ASUMobiCarG11/ASUMobiCarG11/Arduino EX - SH/1.PNG

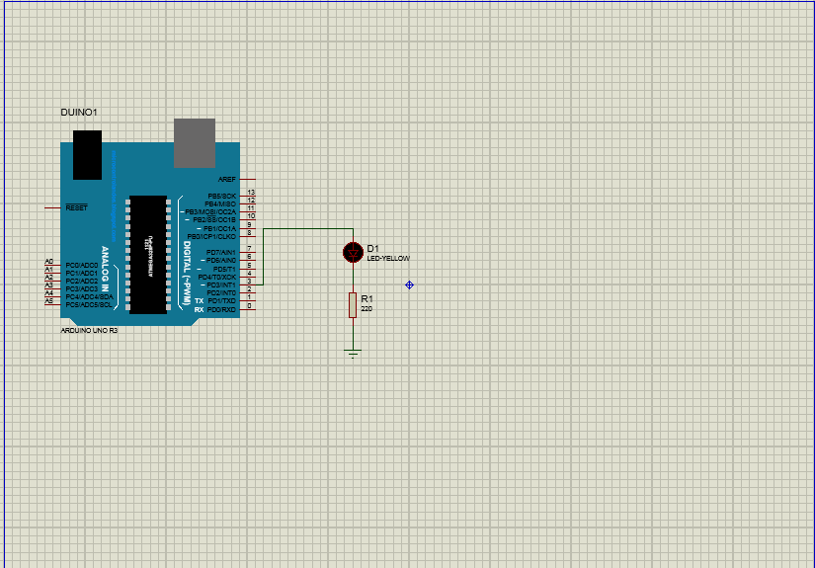
Arduino EX - SH/1.PNG
