ASUMobiCarG11/ASUMobiCarG11/Arduino EX - SH/Q2.PNG

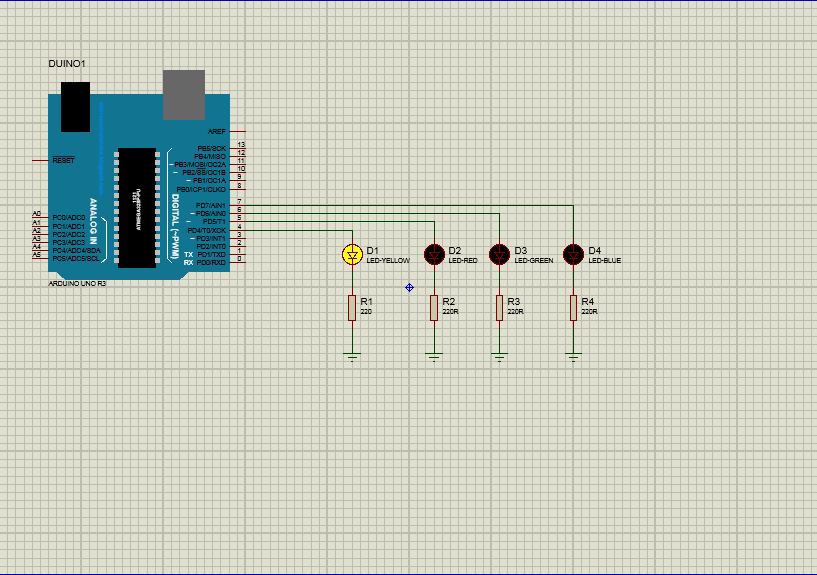
Arduino EX - SH/Q2.PNG
