ASUMobiCarG11/ASUMobiCarG11/Designing the car/re-car-final.jpg

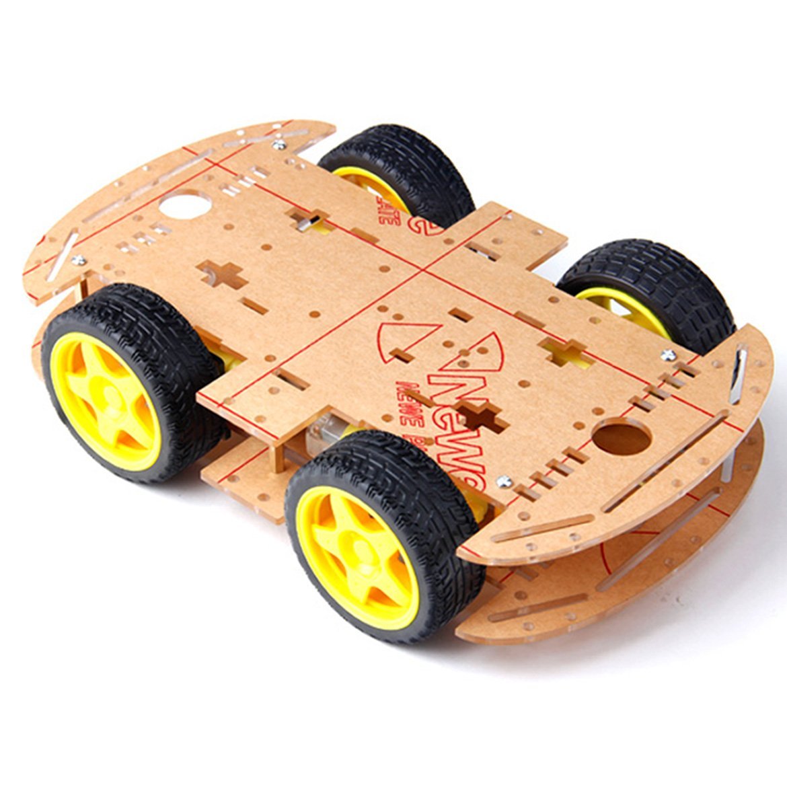
Designing the car/re-car-final.jpg
