ASUMobiCarG11/ASUMobiCarG11/dfrobot-4wd-arduino-mobile-platform-2_2.jpg

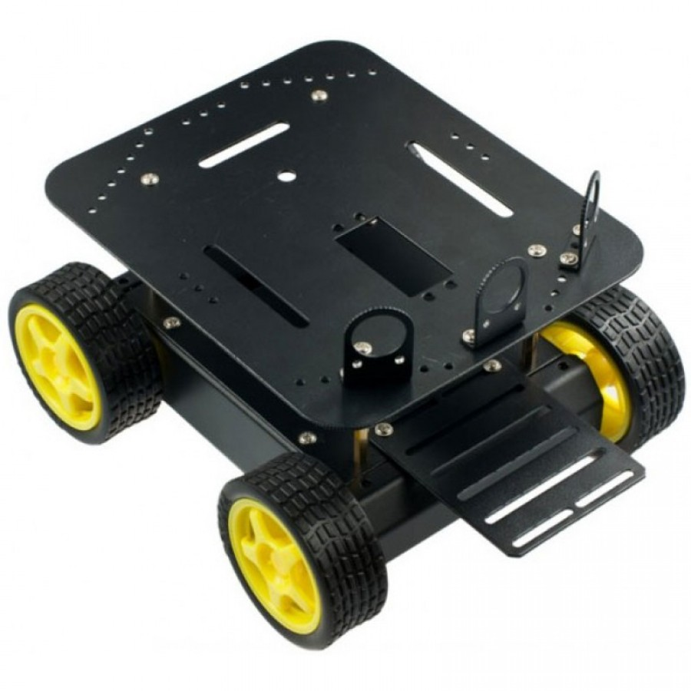
dfrobot-4wd-arduino-mobile-platform-2_2.jpg
