ASUMobiCarG11/ASUMobiCarG11/images.jpg

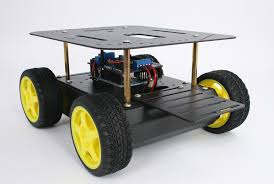
images.jpg
