ASUMobiCarG11/ASUMobiCarG11/Sheet1 Q1.JPG

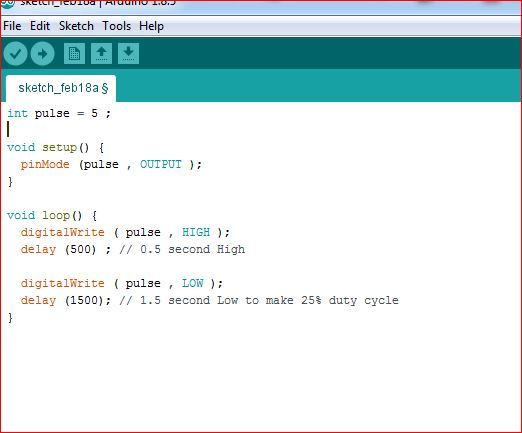
Sheet1 Q1.JPG
