ASUMobiCarG11/ASUMobiCarG11/The code/line follower/all if conditions of line follower.jpg

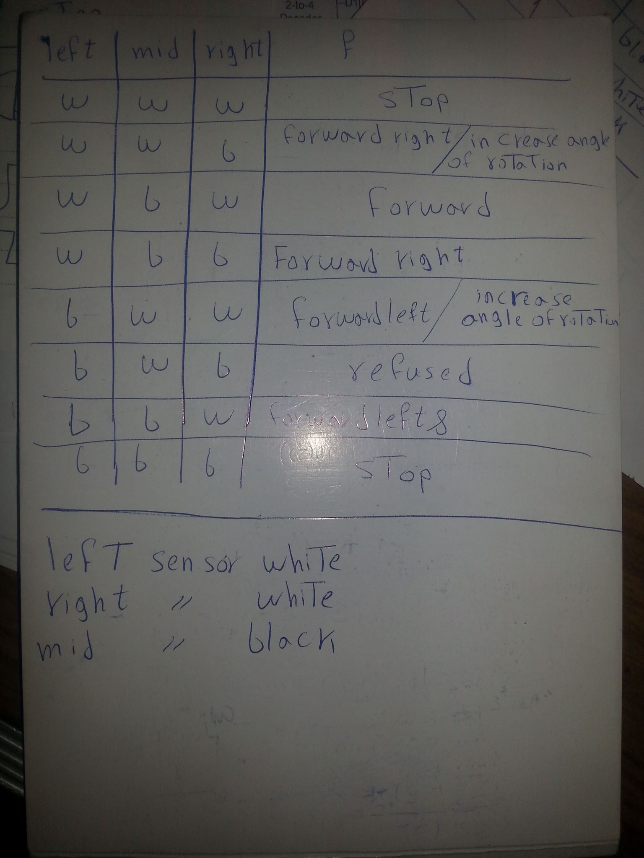
The code/line follower/all if conditions of line follower.jpg
