ASUMobiCarG11/ASUMobiCarG11/Components/3 Line Follower Sensors.jpg

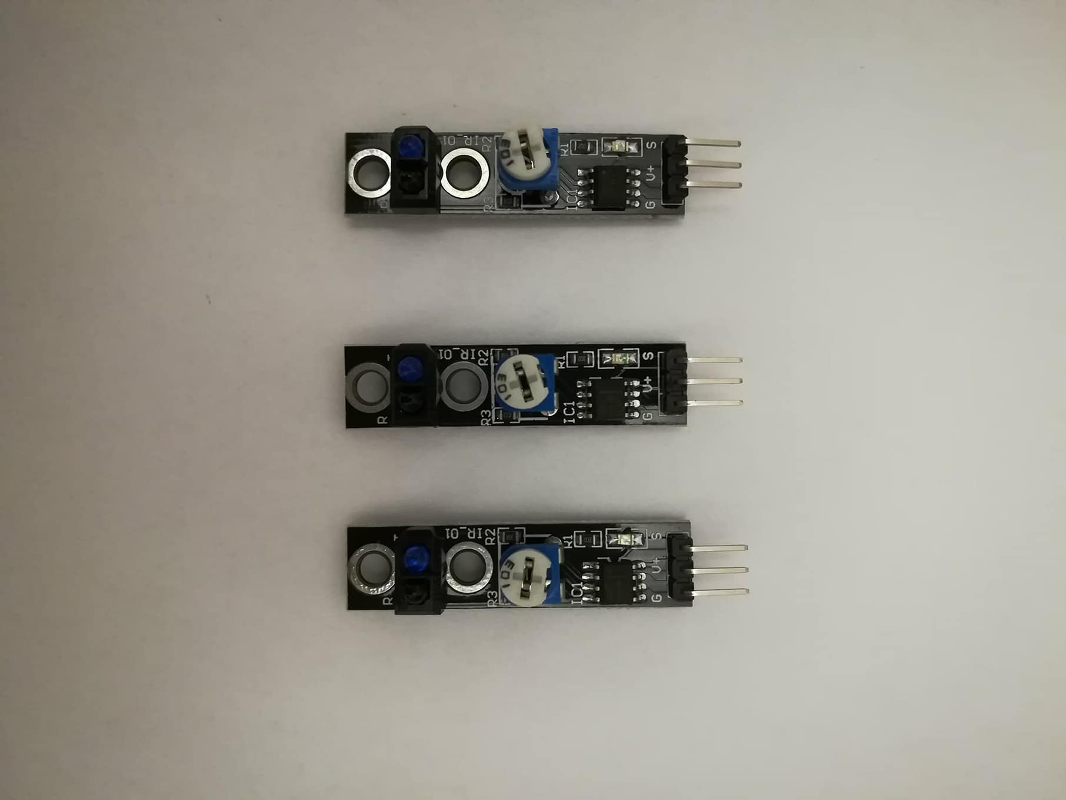
Components/3 Line Follower Sensors.jpg
