ASUMobiCarG11/ASUMobiCarG11/Components/battery.jpeg

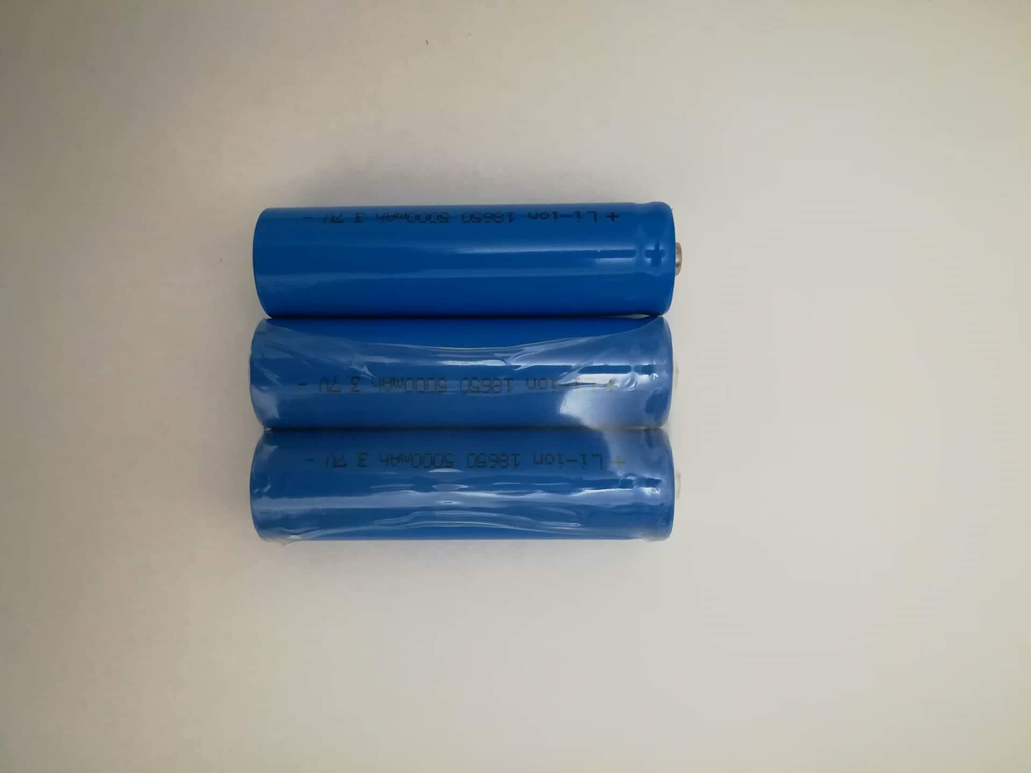
Components/battery.jpeg
