ASUMobiCarG11/ASUMobiCarG11/Components/body of cr.jpeg

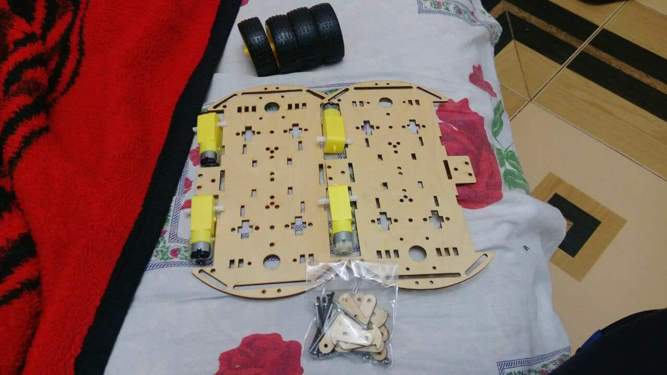
Components/body of cr.jpeg
