ASUMobiCarG11/ASUMobiCarG11/Components/charger.jpeg

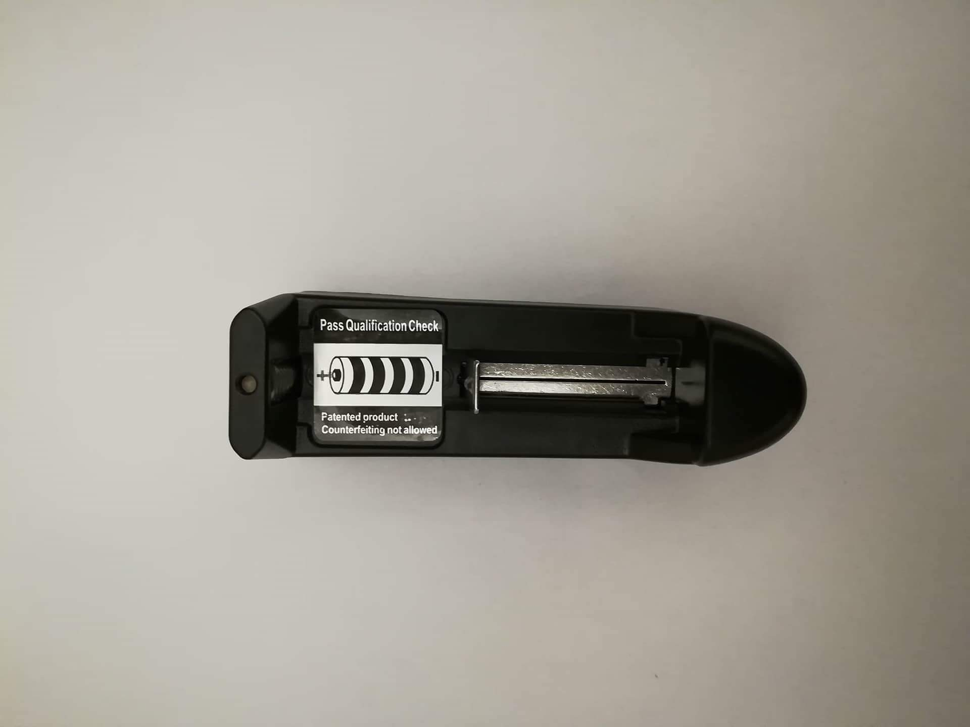
Components/charger.jpeg
