ASUMobiCarG11/ASUMobiCarG11/Components/ultra sonic holder.jpg

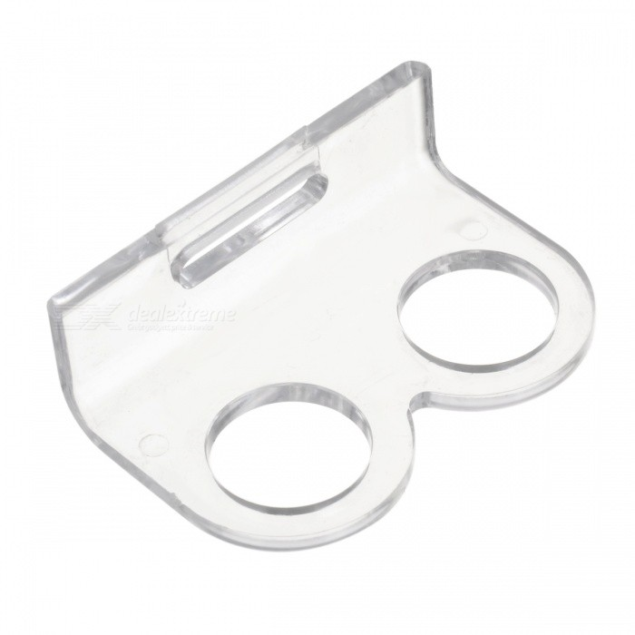
Components/ultra sonic holder.jpg
