ASUMobiCarG11/ASUMobiCarG11/Car installation step by step/instaliing motors to body 1.jpg

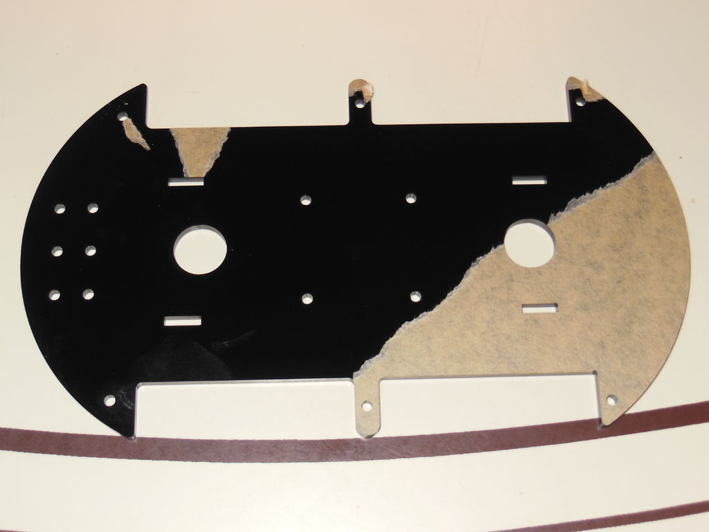
Car installation step by step/instaliing motors to body 1.jpg
