ASUMobiCarG11/ASUMobiCarG11/Car installation step by step/instaliing motors to body 3 invert.jpg

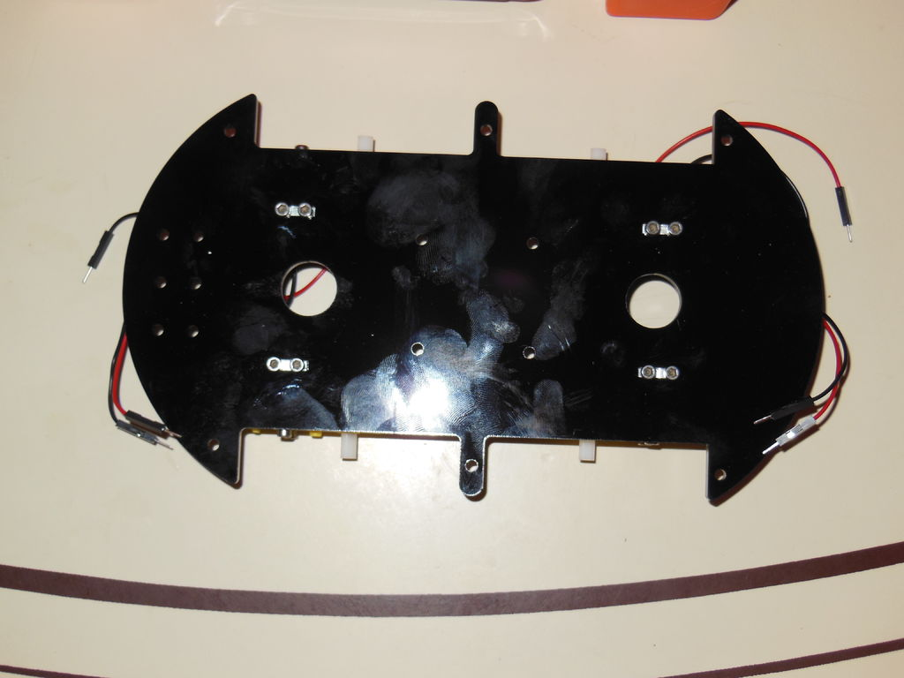
Car installation step by step/instaliing motors to body 3 invert.jpg
