ASUMobiCarG11/ASUMobiCarG11/Car installation step by step/installing arduino uno.jpg

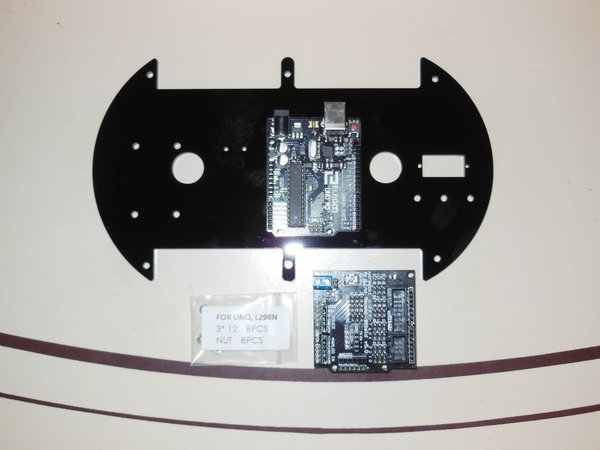
Car installation step by step/installing arduino uno.jpg
