ASUMobiCarG11/ASUMobiCarG11/Car installation step by step/installing battery.jpg

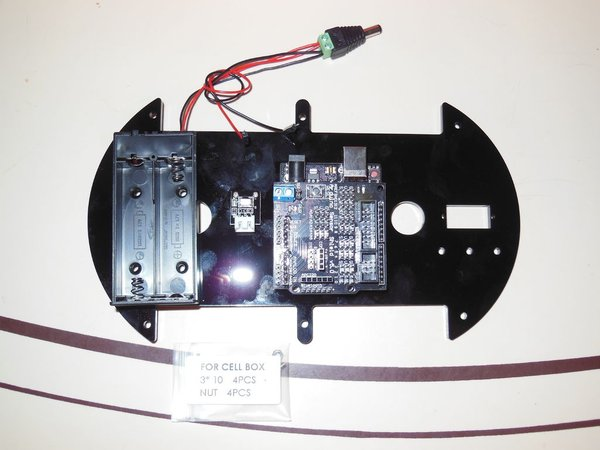
Car installation step by step/installing battery.jpg
