ASUMobiCarG11/ASUMobiCarG11/Car installation step by step/installing blutooth module.jpg

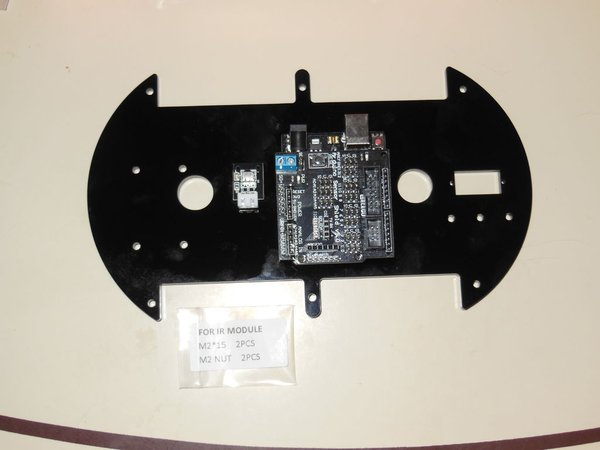
Car installation step by step/installing blutooth module.jpg
