ASUMobiCarG11/ASUMobiCarG11/Car installation step by step/installing line tracker 1.jpg

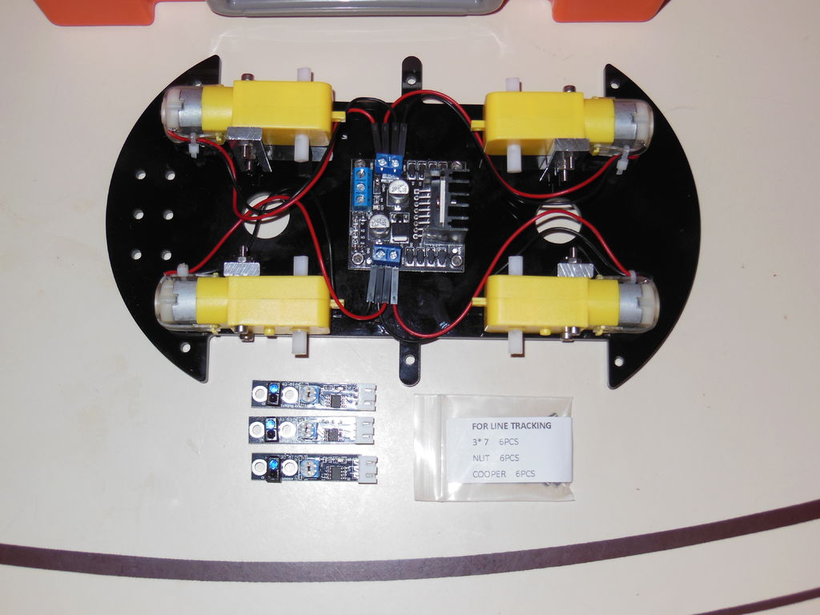
Car installation step by step/installing line tracker 1.jpg
