ASUMobiCarG11/ASUMobiCarG11/Car installation step by step/installing mototr driver 2.jpg

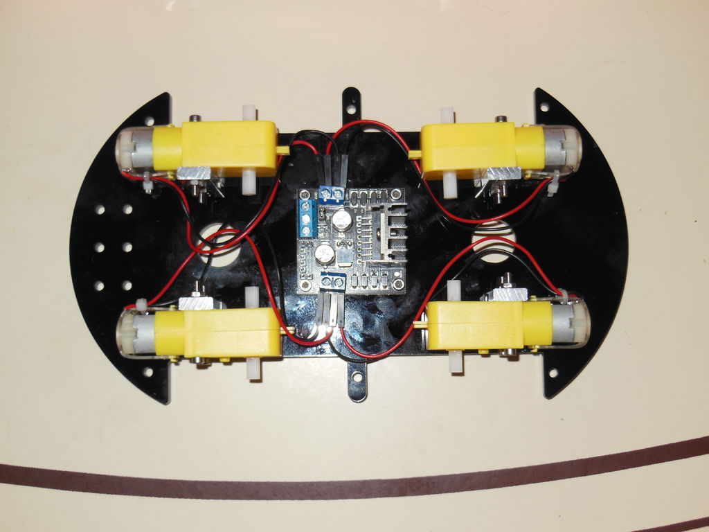
Car installation step by step/installing mototr driver 2.jpg
