ASUMobiCarG11/ASUMobiCarG11/Car installation step by step/ready1.jpg

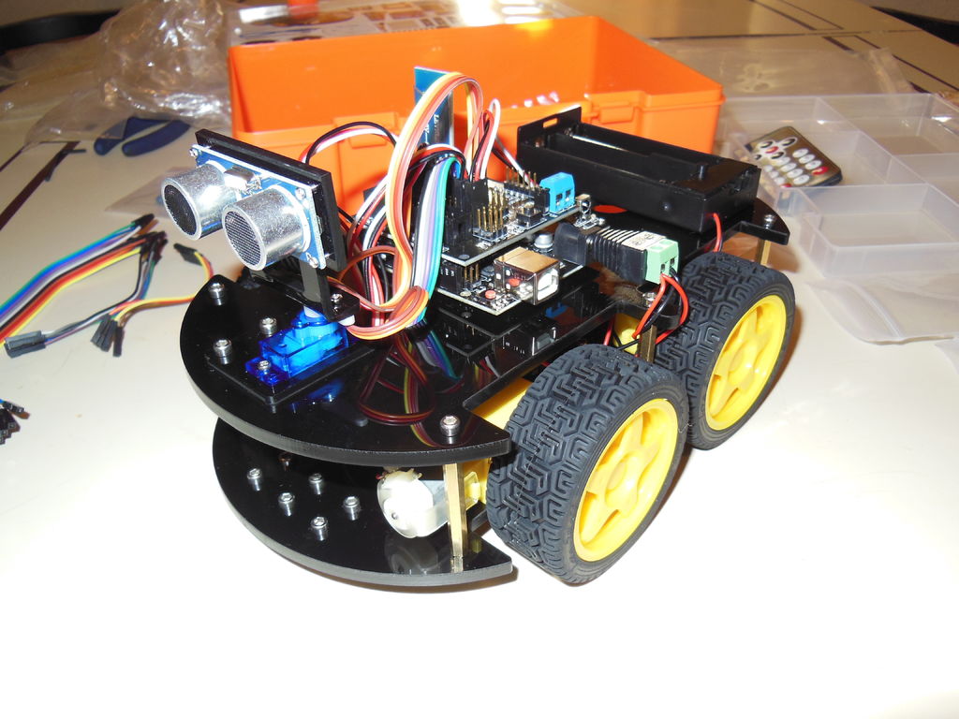
Car installation step by step/ready1.jpg
