ASUMobiCarG11/ASUMobiCarG11/Car installation step by step/ready2.jpg

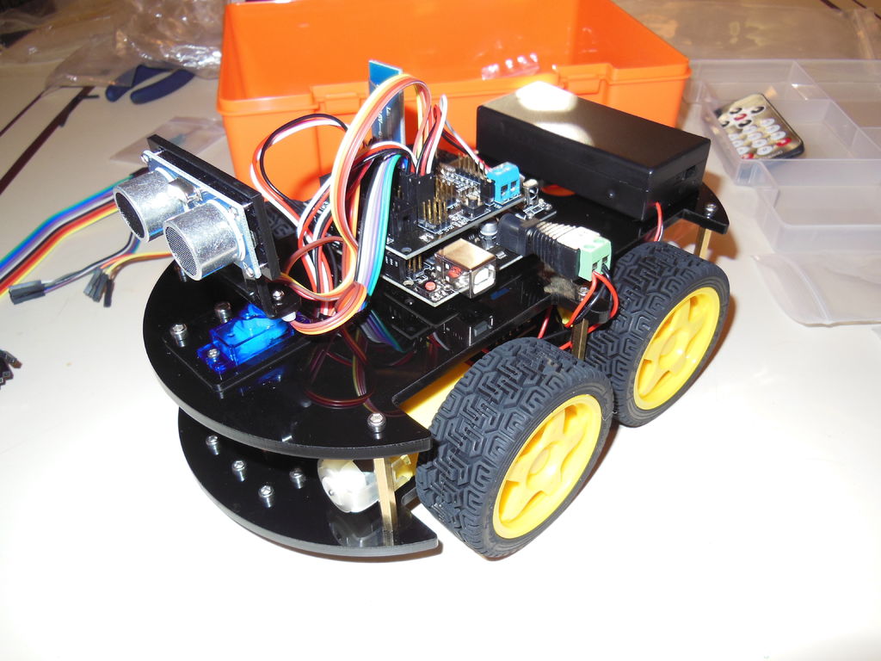
Car installation step by step/ready2.jpg
