ASUMobiCarG11/ASUMobiCarG11/Car installation step by step/ready3.jpg

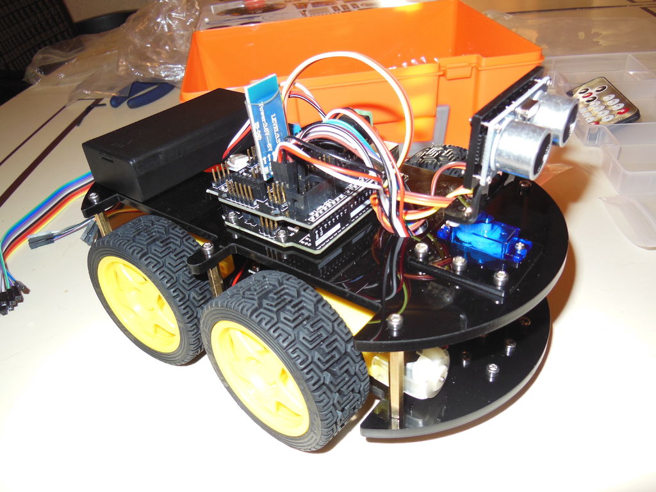
Car installation step by step/ready3.jpg
