ASUMobiCarG11/ASUMobiCarG11/step(1) _design by buttons.png

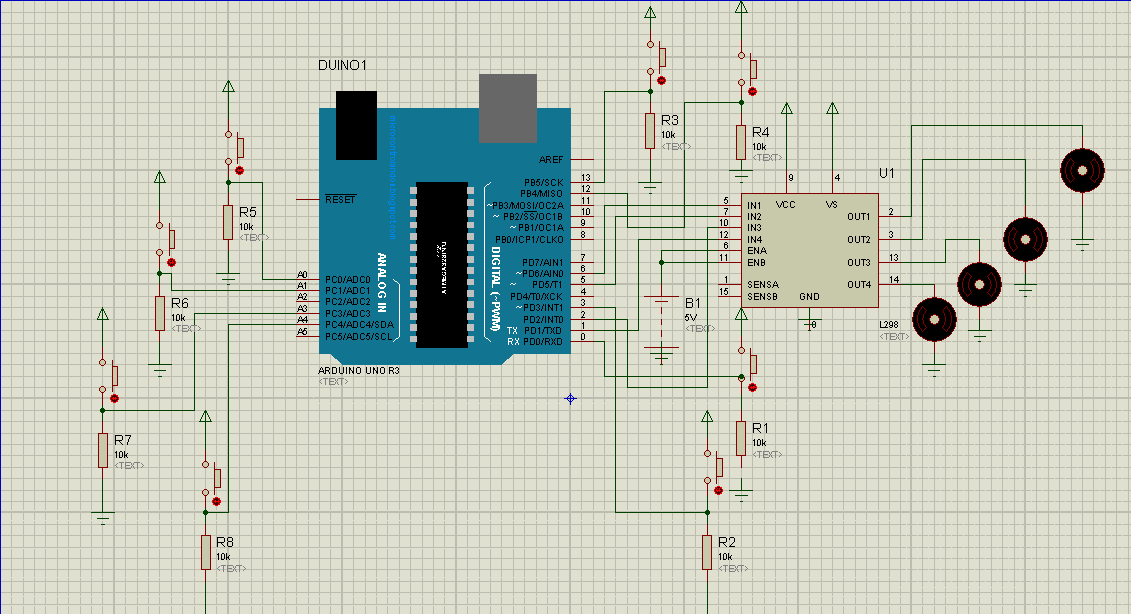
step(1) _design by buttons.png
