ASUMobiCarG11/ASUMobiCarG11/Arduino EX - SH/Sheet__1_Q_1_.ino

int led=10;
void setup() {
  // put your setup code here, to run once:
pinMode(led,OUTPUT);
}

void loop() {
  // put your main code here, to run repeatedly:
digitalWrite(led,HIGH);
delay(500);
digitalWrite(led,LOW);
delay(1500);
}
